codezork/BlueNodes/mobile/bluenodes/src/main/ic_home-web.png

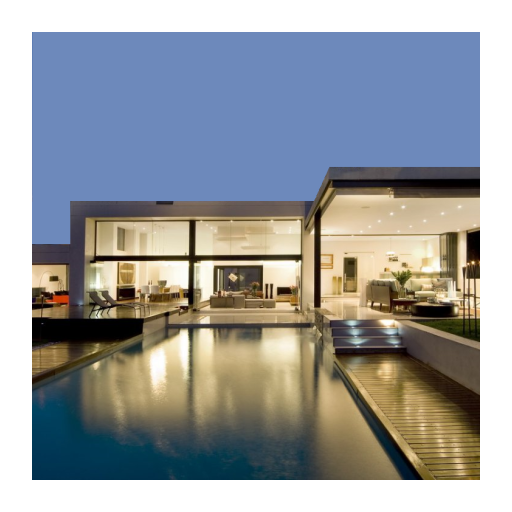
mobile/bluenodes/src/main/ic_home-web.png
