codezork/BlueNodes/pcb/bluenodes_actor52832-19-btm.png

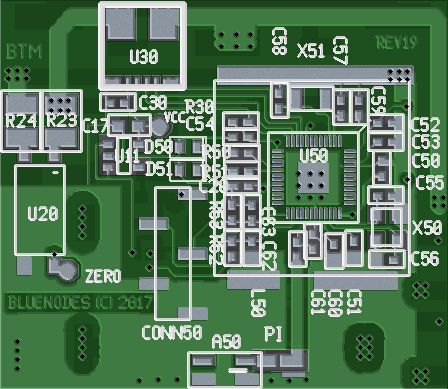
pcb/bluenodes_actor52832-19-btm.png
