codezork/BlueNodes/pictures/IMG_20170207_231757.jpg

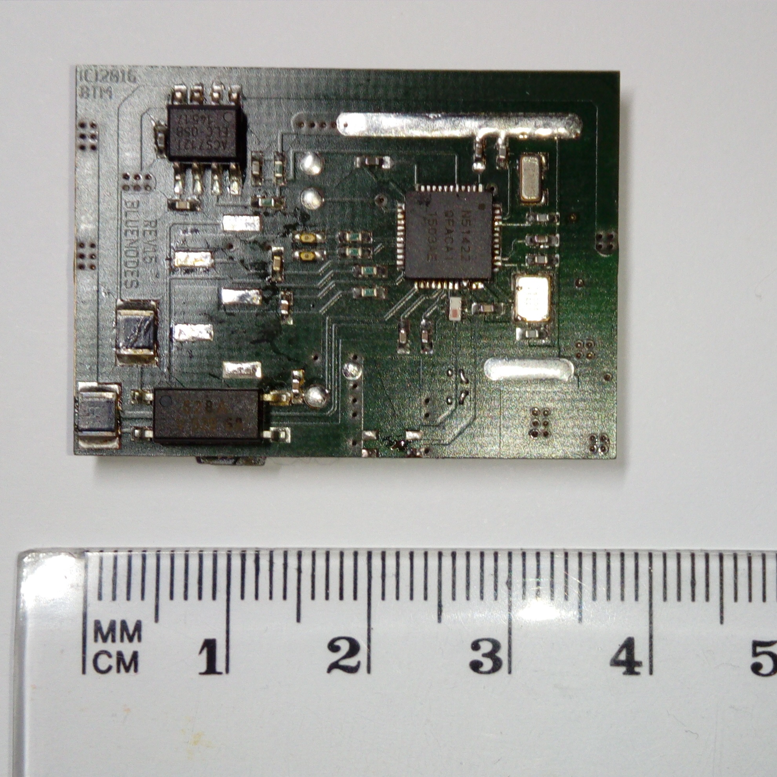
pictures/IMG_20170207_231757.jpg
