codezork/BlueNodes/pictures/IMG_20170207_231932.jpg

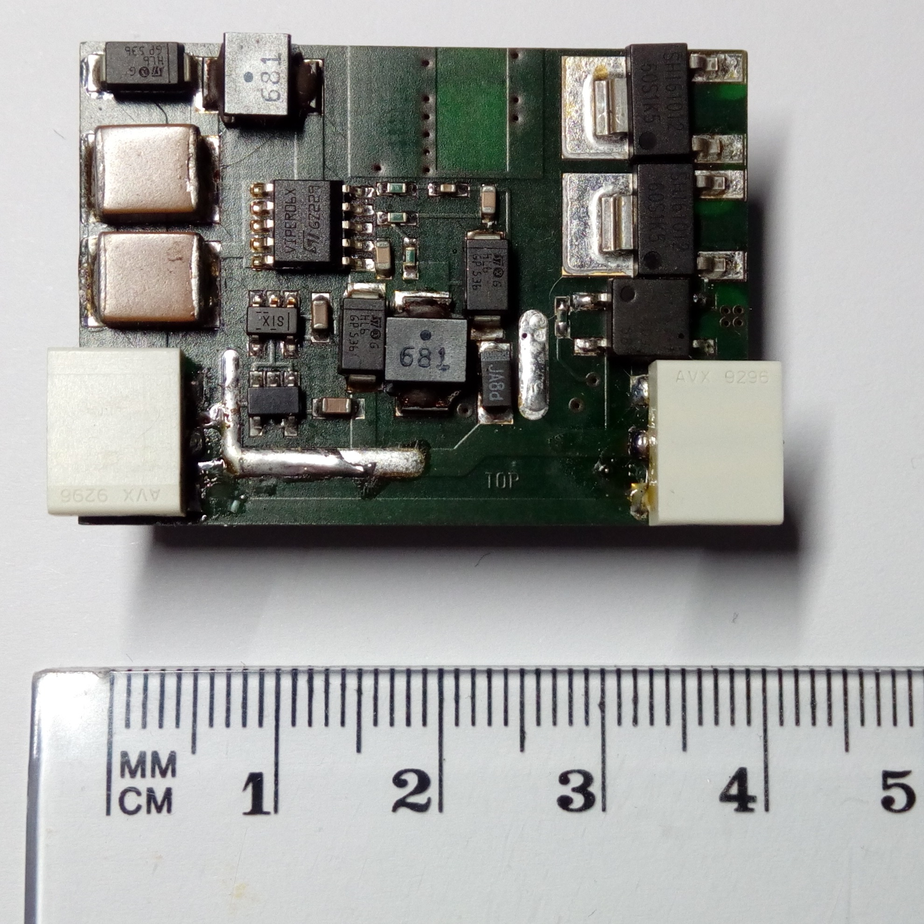
pictures/IMG_20170207_231932.jpg
