codezork/BlueNodes/pictures/IMG_20170207_232309.jpg

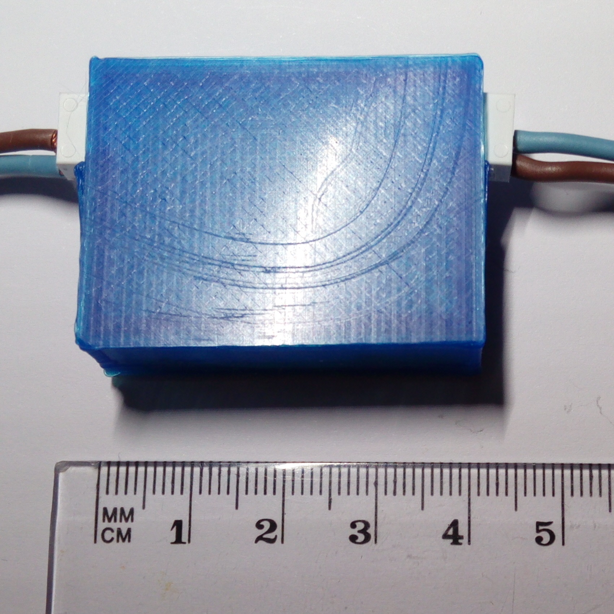
pictures/IMG_20170207_232309.jpg
