codezork/BlueNodes/screenshots/Screenshot_2017-02-15-21-28-17.png

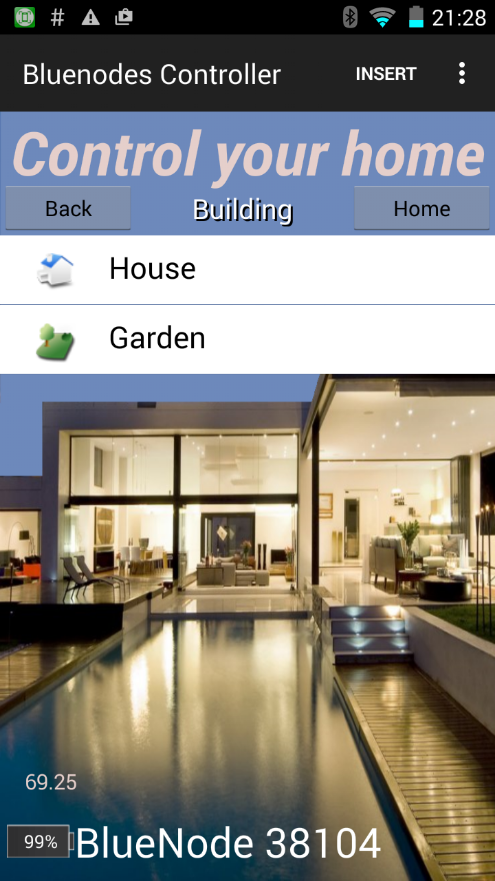
screenshots/Screenshot_2017-02-15-21-28-17.png
