codezork/BlueNodes/screenshots/Screenshot_2017-02-15-21-30-29.png

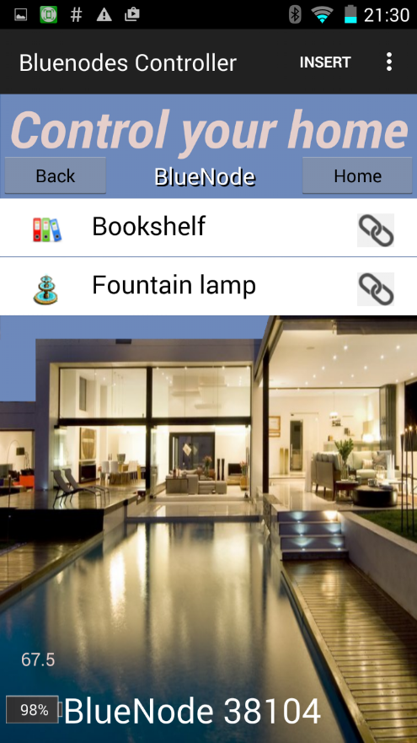
screenshots/Screenshot_2017-02-15-21-30-29.png
