codezork/BlueNodes/screenshots/Screenshot_2017-02-15-21-30-53.png

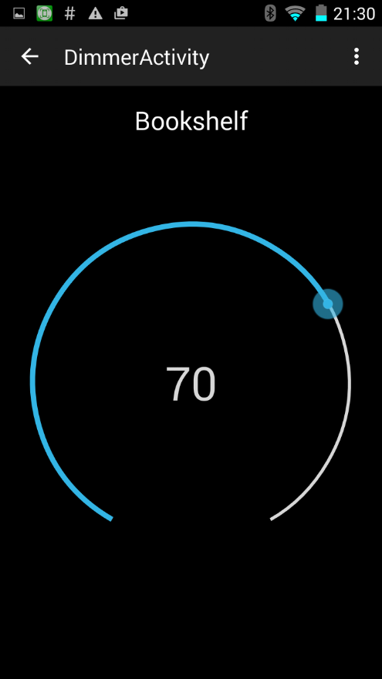
screenshots/Screenshot_2017-02-15-21-30-53.png
