codezork/BlueNodes/screenshots/Screenshot_2017-02-15-21-32-35.png

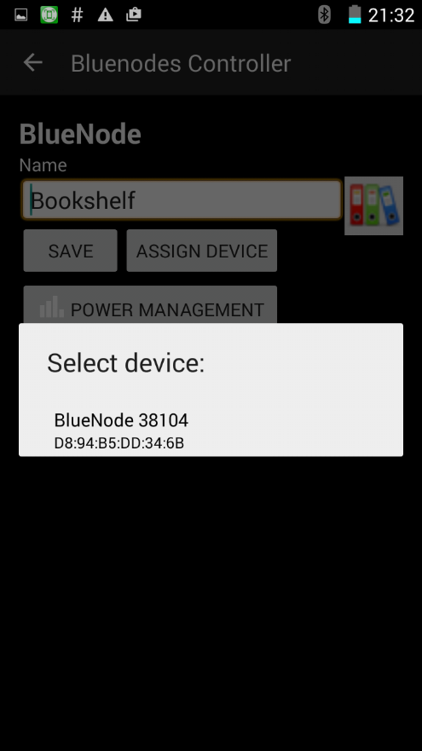
screenshots/Screenshot_2017-02-15-21-32-35.png
