codezork/BlueNodes/screenshots/Screenshot_2017-02-15-21-33-32.png

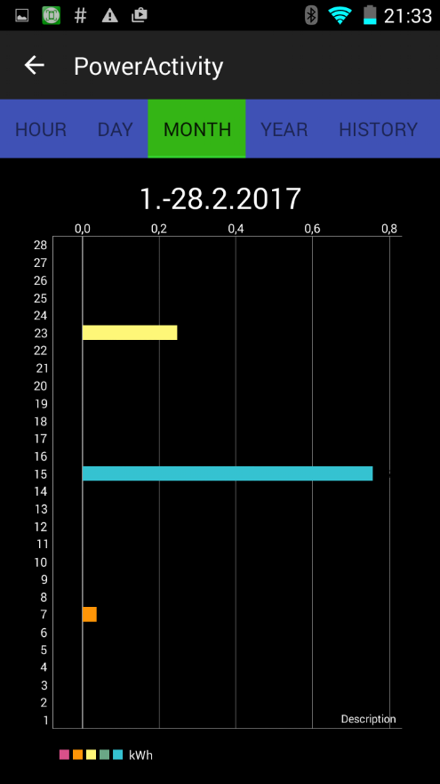
screenshots/Screenshot_2017-02-15-21-33-32.png
