codezork/BlueNodes/screenshots/Screenshot_2017-02-15-21-33-45.png

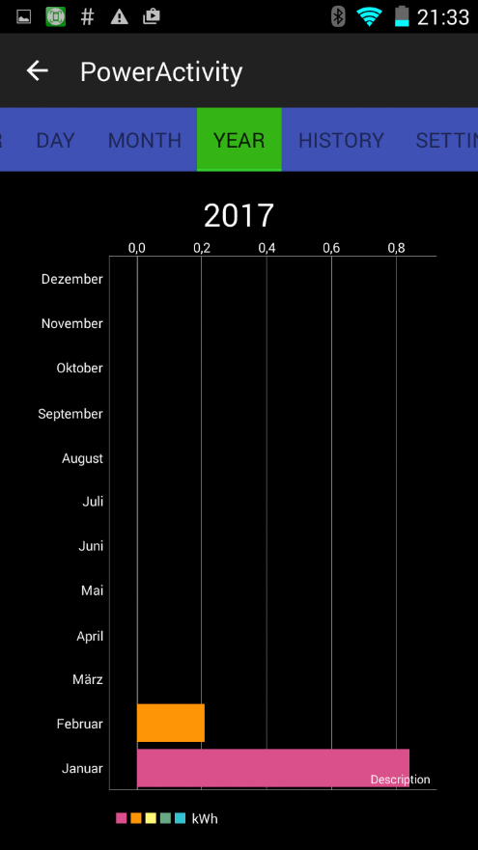
screenshots/Screenshot_2017-02-15-21-33-45.png
