codezork/BlueNodes/screenshots/Screenshot_2017-02-15-21-33-59.png

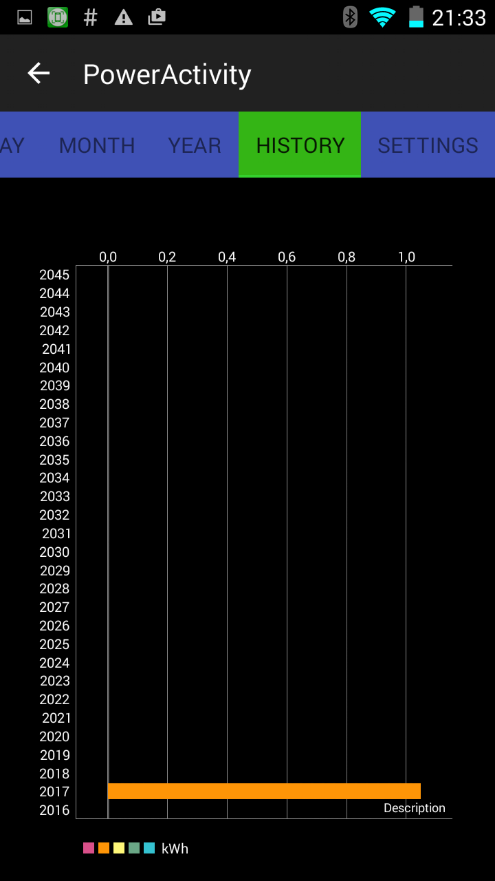
screenshots/Screenshot_2017-02-15-21-33-59.png
