codezork/BlueNodes/screenshots/Screenshot_2017-02-15-21-34-13.png

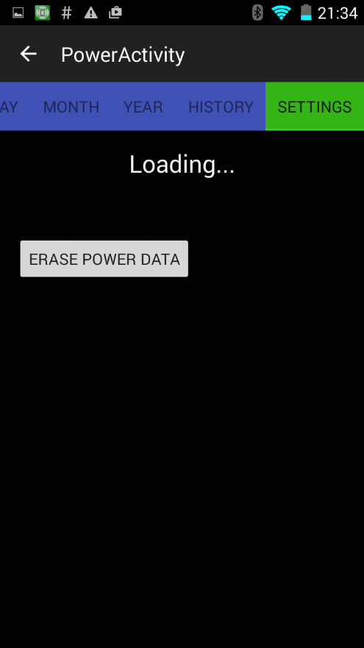
screenshots/Screenshot_2017-02-15-21-34-13.png
