codezork/BlueNodes/screenshots/Screenshot_2017-02-15-21-44-44.png

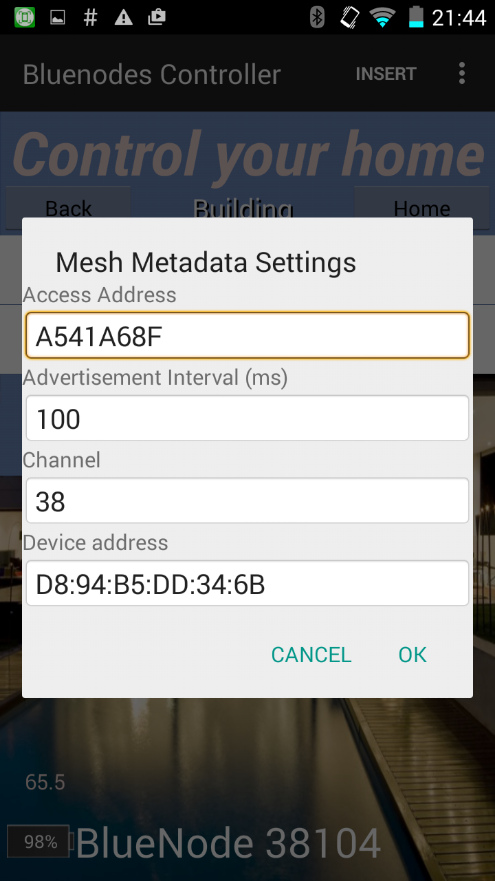
screenshots/Screenshot_2017-02-15-21-44-44.png
