codezork/BlueNodes/firmware/bluenodes_s132_sdk13_085_nrf52/Src/boards.h

/* Copyright (c) 2014 Nordic Semiconductor. All Rights Reserved.
 *
 * The information contained herein is property of Nordic Semiconductor ASA.
 * Terms and conditions of usage are described in detail in NORDIC
 * SEMICONDUCTOR STANDARD SOFTWARE LICENSE AGREEMENT.
 *
 * Licensees are granted free, non-transferable use of the information. NO
 * WARRANTY of ANY KIND is provided. This heading must NOT be removed from
 * the file.
 *
 */
#ifndef BOARDS_H
#define BOARDS_H

#include "nrf_gpio.h"

#if defined(BOARD_PCA10028)
  #include "pca10028.h"
#elif defined(BOARD_PCA10031)
  #include "pca10031.h"
#elif defined(BOARD_BLUENODES)
  #include "bluenodes.h"
#else
#error "Board is not defined"

#endif

#ifdef __cplusplus
extern "C" {
#endif

#define LEDS_OFF(leds_mask) do {  NRF_GPIO->OUTSET = (leds_mask) & (LEDS_MASK & LEDS_INV_MASK); \
                            NRF_GPIO->OUTCLR = (leds_mask) & (LEDS_MASK & ~LEDS_INV_MASK); } while (0)

#define LEDS_ON(leds_mask) do {  NRF_GPIO->OUTCLR = (leds_mask) & (LEDS_MASK & LEDS_INV_MASK); \
                           NRF_GPIO->OUTSET = (leds_mask) & (LEDS_MASK & ~LEDS_INV_MASK); } while (0)

#define LED_IS_ON(leds_mask) ((leds_mask) & (NRF_GPIO->OUT ^ LEDS_INV_MASK) )

#define LEDS_INVERT(leds_mask) do { uint32_t gpio_state = NRF_GPIO->OUT;      \
                              NRF_GPIO->OUTSET = ((leds_mask) & ~gpio_state); \
                              NRF_GPIO->OUTCLR = ((leds_mask) & gpio_state); } while (0)

#define LEDS_CONFIGURE(leds_mask) do { uint32_t pin;                  \
                                  for (pin = 0; pin < 32; pin++) \
                                      if ( (leds_mask) & (1 << pin) )   \
                                          nrf_gpio_cfg_output(pin); } while (0)


#ifdef __cplusplus
}
#endif

#endif
